migoun/mechanical_keyboard_mac/pics/kbpic20180716_184621.jpg

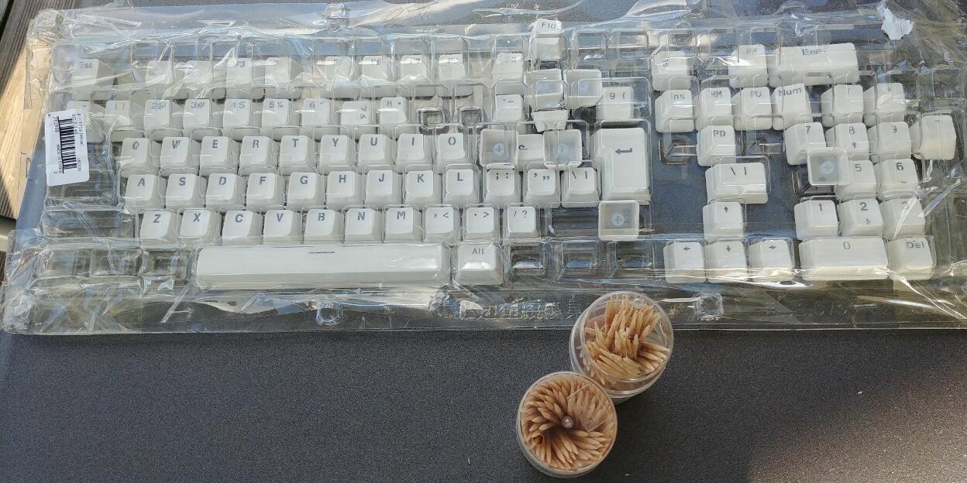
pics/kbpic20180716_184621.jpg
